retrobuiltRyan/IR-Remote-for-PC-Media/ReadMe.ino

/*******************************************************************
=================================================================================
Create a folder named "IR_remote_for_PC_ProMicro32u4" dump these files into it :

IR_remote_for_PC_ProMicro32u4.ino (this is the main program)
profile0.ino
profile1.ino
profile2.ino
profile3.ino

=================================================================================

Ryan's helpful tips for keyboard and mousing macros:

=============== Keyboard Control================================================================================
Keyboard.write();   Sends a keystroke to a connected computer. 
                    This is similar to pressing and releasing a key on your keyboard.
                    Will send a shift command if applicable. Example: Keyboard.write('K') will 
                    automatically do SHIFT + k. 
                    Can also accept ASCII code like this:
                    //Keyboard.write(32); // This is space bar (in decimal)
                    Helpful list of ASCII + decimal keys http://www.asciitable.com/
                    

Keyboard.press();   Best for holding down a key with multi-key commands; like copy/ paste
                    This example is [ctrl] + [shift] + [e] 
                      //Keyboard.press(KEY_LEFT_CTRL);
                      //Keyboard.press(KEY_LEFT_SHIFT);
                      //Keyboard.press('e'); 
                      //delay(100); Keyboard.releaseAll();
                

Keyboard.print();   Sends a keystroke(s)
                    Keyboard.print("stop using aim bot"); // types this in as a char or int! (not a string)!


Keyboard.println(); Sends a keystroke followed by a newline (carriage return)
                     Very practical if you want to type a password and login in one button press!
                     
SOMETIMES, applications are coded to recognize Keyboard.press() and not Keyboard.write() and vice versa.
You might have to experiment. 
// https://github.com/arduino-libraries/Keyboard/blob/master/src/Keyboard.h

=============== Mouse Control================================================================================
Mouse.move(x, y, wheel);  Moves the mouse and or scroll wheel up/down left/right.
                          Range is -128 to +127. units are pixels 
                          -number = left or down
                          +number = right or up

Mouse.press(b);         Presses the mouse button (still need to call release). Replace "b" with:
                        MOUSE_LEFT   //Left Mouse button
                        MOUSE_RIGHT  //Right Mouse button
                        MOUSE_MIDDLE //Middle mouse button
                        MOUSE_ALL    //All three mouse buttons
                        
Mouse.release(b);       Releases the mouse button.

Mouse.click(b);         A quick press and release.

*********************************************************************************************************
Keyboard  Modifiers

#define KEY_LEFT_CTRL     0x80
#define KEY_LEFT_SHIFT    0x81
#define KEY_LEFT_ALT      0x82
#define KEY_LEFT_GUI      0x83
#define KEY_RIGHT_CTRL    0x84
#define KEY_RIGHT_SHIFT   0x85
#define KEY_RIGHT_ALT     0x86
#define KEY_RIGHT_GUI     0x87

// Misc keys
#define KEY_UP_ARROW      0xDA
#define KEY_DOWN_ARROW    0xD9
#define KEY_LEFT_ARROW    0xD8
#define KEY_RIGHT_ARROW   0xD7
#define KEY_BACKSPACE     0xB2
#define KEY_TAB           0xB3
#define KEY_RETURN        0xB0
#define KEY_MENU          0xED // "Keyboard Application" in USB standard
#define KEY_ESC           0xB1
#define KEY_INSERT        0xD1
#define KEY_DELETE        0xD4
#define KEY_PAGE_UP       0xD3
#define KEY_PAGE_DOWN     0xD6
#define KEY_HOME          0xD2
#define KEY_END           0xD5
#define KEY_CAPS_LOCK     0xC1
#define KEY_PRINT_SCREEN  0xCE // Print Screen / SysRq
#define KEY_SCROLL_LOCK   0xCF
#define KEY_PAUSE         0xD0 // Pause / Break

*/
